rayan4444/assembly_line_wearable/REV1 - IMU BREAKOUT/TEST_DATA/TEST_SET_2_unscrewing/az.csv

Az
-0.19482421875
-0.19921875
-0.19140625
-0.20751953125
-0.189453125
-0.189453125
-0.19384765625
-0.2138671875
-0.17822265625
-0.15478515625
-0.16162109375
-0.17431640625
-0.142578125
-0.1796875
-0.0947265625
-0.03955078125
0.01171875
0.078125
0.08837890625
0.09521484375
0.14501953125
0.2041015625
0.31787109375
0.2509765625
0.2939453125
0.36474609375
0.365234375
0.4833984375
0.4892578125
0.50537109375
0.5537109375
0.57763671875
0.61279296875
0.58251953125
0.6171875
0.62744140625
0.64013671875
0.64208984375
0.673828125
0.75390625
0.78173828125
0.77734375
0.67138671875
0.6337890625
0.6083984375
0.64111328125
0.69384765625
0.7548828125
0.8095703125
0.8056640625
0.8212890625
0.81103515625
0.8037109375
0.66015625
0.775390625
0.7783203125
0.72802734375
0.73828125
0.76416015625
0.78076171875
0.78466796875
0.79296875
0.74072265625
0.74853515625
0.775390625
0.88330078125
0.59716796875
0.79541015625
0.72265625
0.80615234375
0.85791015625
0.8330078125
0.82177734375
0.81787109375
0.72509765625
1.24755859375
0.77880859375
0.83984375
0.71240234375
0.7275390625
0.7333984375
0.74365234375
0.62109375
0.69384765625
0.67333984375
0.74609375
0.7998046875
0.77734375
0.70751953125
0.75634765625
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
