rayan4444/assembly_line_wearable/REV1 - IMU BREAKOUT/TEST_DATA/TEST_SET_2_unscrewing/sensor_log.csv

Index | Timestamp | Ax | Ay | Az | Gx | Gy | Gz
1 | 2019-09-03 15:57:00 | 0.93798828125 | -0.08154296875 | -0.19482421875 | 0.7404580152671756 | 0.8091603053435115 | 0.8015267175572519
2 | 2019-09-03 15:57:00 | 0.9345703125 | -0.07958984375 | -0.19921875 | -0.061068702290076333 | 0.732824427480916 | 0.5877862595419847
3 | 2019-09-03 15:57:01 | 0.93359375 | -0.08447265625 | -0.19140625 | 0.9541984732824428 | 1.2213740458015268 | -0.08396946564885496
4 | 2019-09-03 15:57:01 | 0.92919921875 | -0.08203125 | -0.20751953125 | 0.0 | 1.786259541984733 | 0.6564885496183206
5 | 2019-09-03 15:57:01 | 0.93603515625 | -0.080078125 | -0.189453125 | 0.5648854961832062 | 0.9541984732824428 | 0.35877862595419846
6 | 2019-09-03 15:57:01 | 0.93505859375 | -0.08984375 | -0.189453125 | 0.32061068702290074 | 1.2900763358778626 | -1.1603053435114503
7 | 2019-09-03 15:57:01 | 0.9638671875 | -0.0830078125 | -0.19384765625 | 0.1984732824427481 | 2.1603053435114505 | -0.4961832061068702
8 | 2019-09-03 15:57:01 | 0.935546875 | -0.0947265625 | -0.2138671875 | -0.9541984732824428 | 4.358778625954199 | -1.2442748091603053
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
