rayan4444/assembly_line_wearable/REV1 - IMU BREAKOUT/TEST_DATA/TEST_SET_3_Unscrewing/ax.csv

Ax
0.91552734375
0.9072265625
0.94091796875
0.93701171875
0.92578125
0.958984375
0.96435546875
0.919921875
0.9599609375
0.9931640625
0.97705078125
0.95458984375
0.84375
0.88525390625
0.908203125
0.90625
0.8525390625
0.85205078125
0.880859375
0.83935546875
0.7431640625
0.82958984375
0.89892578125
0.8603515625
0.865234375
0.8828125
0.82421875
0.7490234375
0.68603515625
0.6083984375
0.5048828125
0.54833984375
0.36767578125
0.525390625
0.650390625
0.50048828125
0.4443359375
0.404296875
0.4384765625
0.4833984375
0.41796875
0.4013671875
0.4248046875
0.3984375
0.32080078125
0.3623046875
0.32080078125
0.30859375
0.37255859375
0.2919921875
0.3486328125
0.349609375
0.34765625
0.36767578125
0.349609375
0.34375
0.3251953125
0.3193359375
0.3076171875
0.28759765625
0.2763671875
0.265625
0.39697265625
0.40771484375
0.33349609375
0.30810546875
0.25732421875
0.29638671875
0.29150390625
0.29296875
0.11083984375
0.228515625
0.21044921875
0.21044921875
0.18603515625
0.21484375
0.15283203125
0.14111328125
0.33642578125
0.265625
0.18505859375
0.1474609375
0.3193359375
0.33935546875
0.1865234375
0.552734375
0.060546875
0.0107421875
0.5458984375
0.44384765625
0.14599609375
0.40673828125
0.1826171875
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
