rayan4444/assembly_line_wearable/REV1 - IMU BREAKOUT/TEST_DATA/TEST_SET_3_Unscrewing/ay.csv

Ay
0.169921875
0.1689453125
0.1591796875
0.17919921875
0.19140625
0.18896484375
0.1796875
0.220703125
0.1484375
0.14013671875
0.119140625
0.12158203125
0.15771484375
0.138671875
0.119140625
0.1181640625
0.09814453125
0.111328125
0.123046875
0.09765625
0.078125
0.0869140625
0.1025390625
0.0859375
0.052734375
0.07568359375
0.083984375
0.0654296875
-0.0146484375
-0.00341796875
0.00048828125
0.060546875
0.12841796875
0.07763671875
0.15185546875
0.1572265625
0.1591796875
0.1298828125
0.1220703125
0.08984375
0.0234375
0.08740234375
0.1083984375
0.162109375
-0.033203125
0.125
0.10009765625
0.12890625
0.09228515625
0.0986328125
0.12109375
0.09228515625
0.13232421875
0.14892578125
0.1787109375
0.15869140625
0.1240234375
0.09765625
0.1474609375
0.16650390625
0.21240234375
0.29296875
0.23974609375
0.22265625
0.169921875
0.14013671875
0.1689453125
0.1572265625
0.14453125
0.3427734375
0.2265625
0.21826171875
0.22265625
0.2080078125
0.185546875
0.21484375
0.314453125
0.23486328125
0.22021484375
0.23486328125
0.2099609375
0.19921875
0.25341796875
0.27587890625
0.30859375
0.408203125
0.30419921875
0.294921875
0.43994140625
0.38134765625
0.333984375
0.36962890625
0.10888671875
0.8203125
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
