rayan4444/assembly_line_wearable/REV3 - BT_IMU/Firmware/crimson_ble.c

#include "crimson_ble.h"

//includes based on uart example
#include <stdint.h>
#include <string.h>
#include "nrf.h"
#include "nrf_sdh.h"
#include "nrf_sdh_ble.h"
#include "nordic_common.h"
#include "app_error.h"
#include "app_timer.h"

#include "bsp_btn_ble.h"
#include "ble.h"
#include "ble_hci.h"
#include "ble_advdata.h"
#include "ble_advertising.h"
#include "ble_conn_params.h"
#include "ble_err.h"

#include "nrf_ble_gatt.h"
#include "nrf_ble_qwr.h"
#include "ble_nus.h"

#include "nrf_log.h"
#include "nrf_log_ctrl.h"
#include "nrf_log_default_backends.h"

//additional includes for cts_c service
#include "ble_db_discovery.h"
#include "ble_cts_c.h"
#include "peer_manager.h"
#include "peer_manager_handler.h"
#include "nrf_sdh_soc.h"

#define IS_SRVC_CHANGED_CHARACT_PRESENT 0 
#define NRF_BLE_MAX_MTU_SIZE            GATT_MTU_SIZE_DEFAULT 
#define APP_FEATURE_NOT_SUPPORTED       BLE_GATT_STATUS_ATTERR_APP_BEGIN + 2     

#define APP_BLE_CONN_CFG_TAG            1                                           /**< A tag identifying the SoftDevice BLE configuration. */

#define DEVICE_NAME                     "CRIMSON_TEST"                               /**< Name of device. Will be included in the advertising data. */
#define NUS_SERVICE_UUID_TYPE           BLE_UUID_TYPE_VENDOR_BEGIN                  /**< UUID type for the Nordic UART Service (vendor specific). */

#define APP_BLE_OBSERVER_PRIO           3                                           /**< Application's BLE observer priority. You shouldn't need to modify this value. */

#define APP_ADV_INTERVAL                64                                          /**< The advertising interval (in units of 0.625 ms. This value corresponds to 40 ms). */
#define APP_ADV_TIMEOUT_IN_SECONDS      180                                         /**< The advertising timeout (in units of seconds). */

#define APP_ADV_DURATION                18000                                       /**< The advertising duration (180 seconds) in units of 10 milliseconds. */

#define MIN_CONN_INTERVAL               MSEC_TO_UNITS(500, UNIT_1_25_MS)             /**< Minimum acceptable connection interval (20 ms), Connection interval uses 1.25 ms units. */
#define MAX_CONN_INTERVAL               MSEC_TO_UNITS(1000, UNIT_1_25_MS)             /**< Maximum acceptable connection interval (75 ms), Connection interval uses 1.25 ms units. */
#define SLAVE_LATENCY                   0                                           /**< Slave latency. */
#define CONN_SUP_TIMEOUT                MSEC_TO_UNITS(4000, UNIT_10_MS)             /**< Connection supervisory timeout (4 seconds), Supervision Timeout uses 10 ms units. */
#define FIRST_CONN_PARAMS_UPDATE_DELAY  APP_TIMER_TICKS(5000)                       /**< Time from initiating event (connect or start of notification) to first time sd_ble_gap_conn_param_update is called (5 seconds). */
#define NEXT_CONN_PARAMS_UPDATE_DELAY   APP_TIMER_TICKS(30000)                      /**< Time between each call to sd_ble_gap_conn_param_update after the first call (30 seconds). */
#define MAX_CONN_PARAMS_UPDATE_COUNT    3                                           /**< Number of attempts before giving up the connection parameter negotiation. */

// defines for secure connection things
#define SEC_PARAM_TIMEOUT               30                                          /**< Time-out for pairing request or security request (in seconds). */
#define SEC_PARAM_BOND                  1                                           /**< Perform bonding. */
#define SEC_PARAM_MITM                  0                                           /**< Man In The Middle protection requirement. */
#define SEC_PARAM_LESC                  0                                           /**< LE Secure Connections not enabled. */
#define SEC_PARAM_KEYPRESS              0                                           /**< Keypress notifications not enabled. */
#define SEC_PARAM_IO_CAPABILITIES       BLE_GAP_IO_CAPS_NONE                        /**< I/O capabilities. */
#define SEC_PARAM_OOB                   0                                           /**< Out Of Band data availability. */
#define SEC_PARAM_MIN_KEY_SIZE          7                                           /**< Minimum encryption key size. */
#define SEC_PARAM_MAX_KEY_SIZE          16 

#define DEAD_BEEF                       0xDEADBEEF    

BLE_NUS_DEF(m_nus, NRF_SDH_BLE_TOTAL_LINK_COUNT);  /**< BLE NUS service instance. */  
BLE_CTS_C_DEF(m_cts_c);                                                             /**< Current Time service instance. */                               
NRF_BLE_GATT_DEF(m_gatt);                                                           /**< GATT module instance. */
NRF_BLE_QWR_DEF(m_qwr);                                                             /**< Context for the Queued Write module.*/
BLE_ADVERTISING_DEF(m_advertising);
BLE_DB_DISCOVERY_DEF(m_ble_db_discovery);    
NRF_BLE_GQ_DEF(m_ble_gatt_queue,                                                    /**< BLE GATT Queue instance. */
               NRF_SDH_BLE_PERIPHERAL_LINK_COUNT,
               NRF_BLE_GQ_QUEUE_SIZE);                                       /**< DB discovery module instance. */

static ble_nus_t  m_nus;  
static uint16_t   m_conn_handle          = BLE_CONN_HANDLE_INVALID;                 /**< Handle of the current connection. */
static uint16_t   m_ble_nus_max_data_len = BLE_GATT_ATT_MTU_DEFAULT - 3;                        

static pm_peer_id_t m_peer_id;                                                      /**< Device reference handle to the current bonded central. */

static pm_peer_id_t m_whitelist_peers[BLE_GAP_WHITELIST_ADDR_MAX_COUNT];            /**< List of peers currently in the whitelist. */
static uint32_t     m_whitelist_peer_cnt;                                           /**< Number of peers currently in the whitelist. */


// YOUR_JOB: Use UUIDs for service(s) used in your application.
static ble_uuid_t m_adv_uuids[]          =                                          /**< Universally unique service identifier. */
{
    {BLE_UUID_NUS_SERVICE, NUS_SERVICE_UUID_TYPE},
    {BLE_UUID_CURRENT_TIME_SERVICE, BLE_UUID_TYPE_BLE}
};
// #define OUR_SENSOR_TIMER_INTERVAL     APP_TIMER_TICKS(1000, APP_TIMER_PRESCALER)     // 1000 ms intervals

// external functions to keep track of time (nrf_calendar)
void nrf_cal_set_time(uint32_t year, uint32_t month, uint32_t day, uint32_t hour, uint32_t minute, uint32_t second);

uint32_t year, month, day, hour, minute, second;
volatile bool time_synced= false; 
/**@brief Function for assert macro callback.
 *
 * @details This function will be called in case of an assert in the SoftDevice.
 *
 * @warning This handler is an example only and does not fit a final product. You need to analyse
 *          how your product is supposed to react in case of Assert.
 * @warning On assert from the SoftDevice, the system can only recover on reset.
 *
 * @param[in] line_num    Line number of the failing ASSERT call.
 * @param[in] p_file_name File name of the failing ASSERT call.
 */
void assert_nrf_callback(uint16_t line_num, const uint8_t * p_file_name)
{
    app_error_handler(DEAD_BEEF, line_num, p_file_name);
}

/**@brief Fetch the list of peer manager peer IDs.
 *
 * @param[inout] p_peers   The buffer where to store the list of peer IDs.
 * @param[inout] p_size    In: The size of the @p p_peers buffer.
 *                         Out: The number of peers copied in the buffer.
 */
static void peer_list_get(pm_peer_id_t * p_peers, uint32_t * p_size)
{
    pm_peer_id_t peer_id;
    uint32_t     peers_to_copy;

    peers_to_copy = (*p_size < BLE_GAP_WHITELIST_ADDR_MAX_COUNT) ?
                     *p_size : BLE_GAP_WHITELIST_ADDR_MAX_COUNT;

    peer_id = pm_next_peer_id_get(PM_PEER_ID_INVALID);
    *p_size = 0;

    while ((peer_id != PM_PEER_ID_INVALID) && (peers_to_copy--))
    {
        p_peers[(*p_size)++] = peer_id;
        peer_id = pm_next_peer_id_get(peer_id);
    }
}

/**@brief Clear bond information from persistent storage.
 */
static void delete_bonds(void)
{
    ret_code_t err_code;

    NRF_LOG_INFO("Erase bonds!");

    err_code = pm_peers_delete();
    APP_ERROR_CHECK(err_code);
}

/**@brief Function for handling Peer Manager events.
 *
 * @param[in] p_evt  Peer Manager event.
 */
static void pm_evt_handler(pm_evt_t const * p_evt)
{
    ret_code_t err_code;

    pm_handler_on_pm_evt(p_evt);
    pm_handler_flash_clean(p_evt);

    switch (p_evt->evt_id)
    {
        case PM_EVT_CONN_SEC_SUCCEEDED:
        {
            m_peer_id = p_evt->peer_id;

            // Discover peer's services.
            err_code  = ble_db_discovery_start(&m_ble_db_discovery, p_evt->conn_handle);
            APP_ERROR_CHECK(err_code);
        } break;

        case PM_EVT_PEERS_DELETE_SUCCEEDED:
        {
            advertising_start(false);
        } break;

        case PM_EVT_PEER_DATA_UPDATE_SUCCEEDED:
        {
            // Note: You should check on what kind of white list policy your application should use.
            if (     p_evt->params.peer_data_update_succeeded.flash_changed
                 && (p_evt->params.peer_data_update_succeeded.data_id == PM_PEER_DATA_ID_BONDING))
            {
                NRF_LOG_DEBUG("New Bond, add the peer to the whitelist if possible");
                NRF_LOG_DEBUG("\tm_whitelist_peer_cnt %d, MAX_PEERS_WLIST %d",
                               m_whitelist_peer_cnt + 1,
                               BLE_GAP_WHITELIST_ADDR_MAX_COUNT);

                if (m_whitelist_peer_cnt < BLE_GAP_WHITELIST_ADDR_MAX_COUNT)
                {
                    // Bonded to a new peer, add it to the whitelist.
                    m_whitelist_peers[m_whitelist_peer_cnt++] = m_peer_id;

                    // The whitelist has been modified, update it in the Peer Manager.
                    err_code = pm_device_identities_list_set(m_whitelist_peers, m_whitelist_peer_cnt);
                    if (err_code != NRF_ERROR_NOT_SUPPORTED)
                    {
                        APP_ERROR_CHECK(err_code);
                    }

                    err_code = pm_whitelist_set(m_whitelist_peers, m_whitelist_peer_cnt);
                    APP_ERROR_CHECK(err_code);
                }
            }
        } break;

        default:
            break;
    }
}

/**@brief Function for handling the Current Time Service errors.
 *
 * @param[in]  nrf_error  Error code containing information about what went wrong.
 */
static void current_time_error_handler(uint32_t nrf_error)
{
    APP_ERROR_HANDLER(nrf_error);
}

static void current_time_print(ble_cts_c_evt_t * p_evt)
{
    NRF_LOG_INFO("\r\nCurrent Time:");
   
    day  = (uint32_t)(p_evt->params.current_time.exact_time_256.day_date_time.date_time.day);
    printf("day: %ld\n", day);
    
    month = (uint32_t)(p_evt->params.current_time.exact_time_256.day_date_time.date_time.month);
    printf("month: %ld\n", month);

    year= (uint32_t) (p_evt->params.current_time.exact_time_256.day_date_time.date_time.year);
    printf("year: %ld\n", year);

    hour= (uint32_t)(p_evt->params.current_time.exact_time_256.day_date_time.date_time.hours);
    printf("hour: %ld\n",hour );

    minute=(uint32_t)(p_evt->params.current_time.exact_time_256.day_date_time.date_time.minutes);
    printf("minute: %ld\n", minute);

    second=(uint32_t)(p_evt->params.current_time.exact_time_256.day_date_time.date_time.seconds);
    printf("second: %ld\n", second);

    nrf_cal_set_time(year, month, day, hour, minute, second);
}

/**@brief Function for handling the Current Time Service client events.
 *
 * @details This function will be called for all events in the Current Time Service client that
 *          are passed to the application.
 *
 * @param[in] p_evt Event received from the Current Time Service client.
 */
static void on_cts_c_evt(ble_cts_c_t * p_cts, ble_cts_c_evt_t * p_evt)
{
    ret_code_t err_code;

    switch (p_evt->evt_type)
    {
        case BLE_CTS_C_EVT_DISCOVERY_COMPLETE:
            NRF_LOG_INFO("Current Time Service discovered on server.");
            err_code = ble_cts_c_handles_assign(&m_cts_c,
                                                p_evt->conn_handle,
                                                &p_evt->params.char_handles);
            APP_ERROR_CHECK(err_code);
            break;

        case BLE_CTS_C_EVT_DISCOVERY_FAILED:
            NRF_LOG_INFO("Current Time Service not found on server. ");
            // CTS not found in this case we just disconnect. There is no reason to stay
            // in the connection for this simple app since it all wants is to interact with CT
            if (p_evt->conn_handle != BLE_CONN_HANDLE_INVALID)
            {
                err_code = sd_ble_gap_disconnect(p_evt->conn_handle,
                                                 BLE_HCI_REMOTE_USER_TERMINATED_CONNECTION);
                APP_ERROR_CHECK(err_code);
            }
            break;

        case BLE_CTS_C_EVT_DISCONN_COMPLETE:
            NRF_LOG_INFO("Disconnect Complete.");
            break;

        case BLE_CTS_C_EVT_CURRENT_TIME:
            NRF_LOG_INFO("Current Time received.");
            current_time_print(p_evt);
            break;

        case BLE_CTS_C_EVT_INVALID_TIME:
            NRF_LOG_INFO("Invalid Time received.");
            break;

        default:
            break;
    }
}


/**@brief Function for the GAP initialization.
 *
 * @details This function will set up all the necessary GAP (Generic Access Profile) parameters of
 *          the device. It also sets the permissions and appearance.
 */
static void gap_params_init(void)
{
    uint32_t                err_code;
    ble_gap_conn_params_t   gap_conn_params;
    ble_gap_conn_sec_mode_t sec_mode;

    BLE_GAP_CONN_SEC_MODE_SET_OPEN(&sec_mode);

    err_code = sd_ble_gap_device_name_set(&sec_mode,
                                          (const uint8_t *) DEVICE_NAME,
                                          strlen(DEVICE_NAME));
    APP_ERROR_CHECK(err_code);

    memset(&gap_conn_params, 0, sizeof(gap_conn_params));

    gap_conn_params.min_conn_interval = MIN_CONN_INTERVAL;
    gap_conn_params.max_conn_interval = MAX_CONN_INTERVAL;
    gap_conn_params.slave_latency     = SLAVE_LATENCY;
    gap_conn_params.conn_sup_timeout  = CONN_SUP_TIMEOUT;

    err_code = sd_ble_gap_ppcp_set(&gap_conn_params);
    APP_ERROR_CHECK(err_code);
}

/**@brief Function for handling Queued Write Module errors.
 *
 * @details A pointer to this function will be passed to each service which may need to inform the
 *          application about an error.
 *
 * @param[in]   nrf_error   Error code containing information about what went wrong.
 */
static void nrf_qwr_error_handler(uint32_t nrf_error)
{
    APP_ERROR_HANDLER(nrf_error);
}

/**@brief Function for handling the data from the Nordic UART Service.
 *
 * @details This function will process the data received from the Nordic UART BLE Service and send
 *          it to the UART module.
 *
 * @param[in] p_evt       Nordic UART Service event.
 */
/**@snippet [Handling the data received over BLE] */
static void nus_data_handler(ble_nus_evt_t * p_evt)
{

    if (p_evt->type == BLE_NUS_EVT_RX_DATA)
    {
        uint32_t err_code;

        NRF_LOG_DEBUG("Received data from BLE NUS. Writing data on UART.");
        NRF_LOG_HEXDUMP_DEBUG(p_evt->params.rx_data.p_data, p_evt->params.rx_data.length);

        for (uint32_t i = 0; i < p_evt->params.rx_data.length; i++)
        {
            do
            {
                err_code = app_uart_put(p_evt->params.rx_data.p_data[i]);
                if ((err_code != NRF_SUCCESS) && (err_code != NRF_ERROR_BUSY))
                {
                    NRF_LOG_ERROR("Failed receiving NUS message. Error 0x%x. ", err_code);
                    APP_ERROR_CHECK(err_code);
                }
            } while (err_code == NRF_ERROR_BUSY);
        }
        if (p_evt->params.rx_data.p_data[p_evt->params.rx_data.length - 1] == '\r')
        {
            while (app_uart_put('\n') == NRF_ERROR_BUSY);
        }
    }

}
/**@snippet [Handling the data received over BLE] */


/**@brief   Function for handling app_uart events.
 *
 * @details This function will receive a single character from the app_uart module and append it to
 *          a string. The string will be be sent over BLE when the last character received was a
 *          'new line' '\n' (hex 0x0A) or if the string has reached the maximum data length.
 */
/**@snippet [Handling the data received over UART] */
void uart_event_handle(app_uart_evt_t * p_event)
{
    static uint8_t data_array[BLE_NUS_MAX_DATA_LEN];
    static uint8_t index = 0;
    uint32_t       err_code;

    switch (p_event->evt_type)
    {
        case APP_UART_DATA_READY:
            UNUSED_VARIABLE(app_uart_get(&data_array[index]));
            index++;

            if ((data_array[index - 1] == '\n') ||
                (data_array[index - 1] == '\r') ||
                (index >= m_ble_nus_max_data_len))
            {
                if (index > 1)
                {
                    NRF_LOG_DEBUG("Ready to send data over BLE NUS");
                    NRF_LOG_HEXDUMP_DEBUG(data_array, index);

                    do
                    {
                        uint16_t length = (uint16_t)index;
                        err_code = ble_nus_data_send(&m_nus, data_array, &length, m_conn_handle);
                        if ((err_code != NRF_ERROR_INVALID_STATE) &&
                            (err_code != NRF_ERROR_RESOURCES) &&
                            (err_code != NRF_ERROR_NOT_FOUND))
                        {
                            APP_ERROR_CHECK(err_code);
                        }
                    } while (err_code == NRF_ERROR_RESOURCES);
                }

                index = 0;
            }
            break;

        case APP_UART_COMMUNICATION_ERROR:
            APP_ERROR_HANDLER(p_event->data.error_communication);
            break;

        case APP_UART_FIFO_ERROR:
            APP_ERROR_HANDLER(p_event->data.error_code);
            break;

        default:
            break;
    }
}
/**@snippet [Handling the data received over UART] */

/**@brief Function for initializing services that will be used by the application.
 */
static void services_init(void)
{
    uint32_t           err_code;
    ble_nus_init_t     nus_init;
    ble_cts_c_init_t   cts_init = {0};
    nrf_ble_qwr_init_t qwr_init = {0};

    // Initialize Queued Write Module.
    qwr_init.error_handler = nrf_qwr_error_handler;

    err_code = nrf_ble_qwr_init(&m_qwr, &qwr_init);
    APP_ERROR_CHECK(err_code);

    // Initialize CTS.
    cts_init.evt_handler   = on_cts_c_evt;
    cts_init.error_handler = current_time_error_handler;
    cts_init.p_gatt_queue  = &m_ble_gatt_queue;
    err_code               = ble_cts_c_init(&m_cts_c, &cts_init);
    APP_ERROR_CHECK(err_code);

    // Initialize NUS.
    memset(&nus_init, 0, sizeof(nus_init));

    nus_init.data_handler = nus_data_handler;

    err_code = ble_nus_init(&m_nus, &nus_init);
    APP_ERROR_CHECK(err_code);

}

/**@brief Function for handling an event from the Connection Parameters Module.
 *
 * @details This function will be called for all events in the Connection Parameters Module
 *          which are passed to the application.
 *
 * @note All this function does is to disconnect. This could have been done by simply setting
 *       the disconnect_on_fail config parameter, but instead we use the event handler
 *       mechanism to demonstrate its use.
 *
 * @param[in] p_evt  Event received from the Connection Parameters Module.
 */
static void on_conn_params_evt(ble_conn_params_evt_t * p_evt)
{
    uint32_t err_code;

    if (p_evt->evt_type == BLE_CONN_PARAMS_EVT_FAILED)
    {
        err_code = sd_ble_gap_disconnect(m_conn_handle, BLE_HCI_CONN_INTERVAL_UNACCEPTABLE);
        APP_ERROR_CHECK(err_code);
    }
}

/**@brief Function for handling errors from the Connection Parameters module.
 *
 * @param[in] nrf_error  Error code containing information about what went wrong.
 */
static void conn_params_error_handler(uint32_t nrf_error)
{
    APP_ERROR_HANDLER(nrf_error);
}


/**@brief Function for initializing the Connection Parameters module.
 */
static void conn_params_init(void)
{
    uint32_t               err_code;
    ble_conn_params_init_t cp_init;

    memset(&cp_init, 0, sizeof(cp_init));

    cp_init.p_conn_params                  = NULL;
    cp_init.first_conn_params_update_delay = FIRST_CONN_PARAMS_UPDATE_DELAY;
    cp_init.next_conn_params_update_delay  = NEXT_CONN_PARAMS_UPDATE_DELAY;
    cp_init.max_conn_params_update_count   = MAX_CONN_PARAMS_UPDATE_COUNT;
    cp_init.start_on_notify_cccd_handle    = BLE_GATT_HANDLE_INVALID;
    cp_init.disconnect_on_fail             = false;
    cp_init.evt_handler                    = on_conn_params_evt;
    cp_init.error_handler                  = conn_params_error_handler;

    err_code = ble_conn_params_init(&cp_init);
    APP_ERROR_CHECK(err_code);
}

/**@brief Function for handling Database Discovery events.
 *
 * @details This function is a callback function to handle events from the database discovery module.
 *          Depending on the UUIDs that are discovered, this function should forward the events
 *          to their respective service instances.
 *
 * @param[in] p_event  Pointer to the database discovery event.
 */
static void db_disc_handler(ble_db_discovery_evt_t * p_evt)
{
    ble_cts_c_on_db_disc_evt(&m_cts_c, p_evt);
}

/**@brief Function for putting the chip into sleep mode.
 *
 * @note This function will not return.
 */
static void sleep_mode_enter(void)
{
    uint32_t err_code = bsp_indication_set(BSP_INDICATE_IDLE);
    APP_ERROR_CHECK(err_code);

    // Prepare wakeup buttons.
    err_code = bsp_btn_ble_sleep_mode_prepare();
    APP_ERROR_CHECK(err_code);

    // Go to system-off mode (this function will not return; wakeup will cause a reset).
    err_code = sd_power_system_off();
    APP_ERROR_CHECK(err_code);
}

/**@brief Function for handling advertising events.
 *
 * @details This function will be called for advertising events which are passed to the application.
 *
 * @param[in] ble_adv_evt  Advertising event.
 */
static void on_adv_evt(ble_adv_evt_t ble_adv_evt)
{
    uint32_t err_code;

    switch (ble_adv_evt)
    {
        case BLE_ADV_EVT_FAST:
            err_code = bsp_indication_set(BSP_INDICATE_ADVERTISING);
            APP_ERROR_CHECK(err_code);
            break;

        case BLE_ADV_EVT_SLOW:
            NRF_LOG_INFO("Slow advertising");
            err_code = bsp_indication_set(BSP_INDICATE_ADVERTISING_SLOW);
            APP_ERROR_CHECK(err_code);
            break;

        case BLE_ADV_EVT_FAST_WHITELIST:
            NRF_LOG_INFO("Fast advertising with WhiteList");
            err_code = bsp_indication_set(BSP_INDICATE_ADVERTISING_WHITELIST);
            APP_ERROR_CHECK(err_code);
            break;
        
        case BLE_ADV_EVT_SLOW_WHITELIST:
            NRF_LOG_INFO("Slow advertising with WhiteList");
            err_code = bsp_indication_set(BSP_INDICATE_ADVERTISING_WHITELIST);
            APP_ERROR_CHECK(err_code);
            err_code = ble_advertising_restart_without_whitelist(&m_advertising);
            APP_ERROR_CHECK(err_code);
            break;

        case BLE_ADV_EVT_IDLE:
            sleep_mode_enter();
            break;
        
        case BLE_ADV_EVT_WHITELIST_REQUEST:
        {
            ble_gap_addr_t whitelist_addrs[BLE_GAP_WHITELIST_ADDR_MAX_COUNT];
            ble_gap_irk_t  whitelist_irks[BLE_GAP_WHITELIST_ADDR_MAX_COUNT];
            uint32_t       addr_cnt = BLE_GAP_WHITELIST_ADDR_MAX_COUNT;
            uint32_t       irk_cnt  = BLE_GAP_WHITELIST_ADDR_MAX_COUNT;

            err_code = pm_whitelist_get(whitelist_addrs, &addr_cnt,
                                        whitelist_irks,  &irk_cnt);
            APP_ERROR_CHECK(err_code);
            NRF_LOG_DEBUG("pm_whitelist_get returns %d addr in whitelist and %d irk whitelist",
                           addr_cnt,
                           irk_cnt);

            // Apply the whitelist.
            err_code = ble_advertising_whitelist_reply(&m_advertising,
                                                       whitelist_addrs,
                                                       addr_cnt,
                                                       whitelist_irks,
                                                       irk_cnt);
            APP_ERROR_CHECK(err_code);
        }
        break;


        default:
            break;
    }
}

/**@brief Function for handling BLE events.
 *
 * @param[in]   p_ble_evt   Bluetooth stack event.
 * @param[in]   p_context   Unused.
 */
static void ble_evt_handler(ble_evt_t const * p_ble_evt, void * p_context)
{
    uint32_t err_code;
    pm_handler_secure_on_connection(p_ble_evt);

    switch (p_ble_evt->header.evt_id)
    {
        case BLE_GAP_EVT_CONNECTED:
            NRF_LOG_INFO("Connected");
            err_code = bsp_indication_set(BSP_INDICATE_CONNECTED);
            APP_ERROR_CHECK(err_code);
            m_conn_handle = p_ble_evt->evt.gap_evt.conn_handle;
            err_code = nrf_ble_qwr_conn_handle_assign(&m_qwr, m_conn_handle);
            APP_ERROR_CHECK(err_code);
            break;

        case BLE_GAP_EVT_DISCONNECTED:
            NRF_LOG_INFO("Disconnected");
            // LED indication will be changed when advertising starts.
            if (p_ble_evt->evt.gap_evt.conn_handle == m_cts_c.conn_handle)
            {

                m_cts_c.conn_handle = BLE_CONN_HANDLE_INVALID;
            } 
            m_conn_handle = BLE_CONN_HANDLE_INVALID;

            break;

        case BLE_GAP_EVT_PHY_UPDATE_REQUEST:
        {
            NRF_LOG_DEBUG("PHY update request.");
            ble_gap_phys_t const phys =
            {
                .rx_phys = BLE_GAP_PHY_AUTO,
                .tx_phys = BLE_GAP_PHY_AUTO,
            };
            err_code = sd_ble_gap_phy_update(p_ble_evt->evt.gap_evt.conn_handle, &phys);
            APP_ERROR_CHECK(err_code);
        } break;

        // case BLE_GAP_EVT_SEC_PARAMS_REQUEST:
        //     // Pairing not supported
        //     err_code = sd_ble_gap_sec_params_reply(m_conn_handle, BLE_GAP_SEC_STATUS_PAIRING_NOT_SUPP, NULL, NULL);
        //     APP_ERROR_CHECK(err_code);
        //     break;

        case BLE_GATTS_EVT_SYS_ATTR_MISSING:
            // No system attributes have been stored.
            err_code = sd_ble_gatts_sys_attr_set(m_conn_handle, NULL, 0, 0);
            APP_ERROR_CHECK(err_code);
            break;

        case BLE_GATTC_EVT_TIMEOUT:
            // Disconnect on GATT Client timeout event.
            err_code = sd_ble_gap_disconnect(p_ble_evt->evt.gattc_evt.conn_handle,
                                             BLE_HCI_REMOTE_USER_TERMINATED_CONNECTION);
            APP_ERROR_CHECK(err_code);
            break;

        case BLE_GATTS_EVT_TIMEOUT:
            // Disconnect on GATT Server timeout event.
            err_code = sd_ble_gap_disconnect(p_ble_evt->evt.gatts_evt.conn_handle,
                                             BLE_HCI_REMOTE_USER_TERMINATED_CONNECTION);
            APP_ERROR_CHECK(err_code);
            break;

        case BLE_EVT_USER_MEM_REQUEST:
            err_code = sd_ble_user_mem_reply(p_ble_evt->evt.gattc_evt.conn_handle, NULL);
            APP_ERROR_CHECK(err_code);
            break; // BLE_EVT_USER_MEM_REQUEST
        
        case BLE_GATTS_EVT_RW_AUTHORIZE_REQUEST:
        {
            ble_gatts_evt_rw_authorize_request_t  req;
            ble_gatts_rw_authorize_reply_params_t auth_reply;

            req = p_ble_evt->evt.gatts_evt.params.authorize_request;

            if (req.type != BLE_GATTS_AUTHORIZE_TYPE_INVALID)
            {
                if ((req.request.write.op == BLE_GATTS_OP_PREP_WRITE_REQ)     ||
                    (req.request.write.op == BLE_GATTS_OP_EXEC_WRITE_REQ_NOW) ||
                    (req.request.write.op == BLE_GATTS_OP_EXEC_WRITE_REQ_CANCEL))
                {
                    if (req.type == BLE_GATTS_AUTHORIZE_TYPE_WRITE)
                    {
                        auth_reply.type = BLE_GATTS_AUTHORIZE_TYPE_WRITE;
                    }
                    else
                    {
                        auth_reply.type = BLE_GATTS_AUTHORIZE_TYPE_READ;
                    }
                    auth_reply.params.write.gatt_status = APP_FEATURE_NOT_SUPPORTED;
                    err_code = sd_ble_gatts_rw_authorize_reply(p_ble_evt->evt.gatts_evt.conn_handle,
                                                               &auth_reply);
                    APP_ERROR_CHECK(err_code);
                }
            }
        } break; // BLE_GATTS_EVT_RW_AUTHORIZE_REQUEST


        default:
            // No implementation needed.
            break;
    }
}


/**@brief Function for the SoftDevice initialization.
 *
 * @details This function initializes the SoftDevice and the BLE event interrupt.
 */
static void ble_stack_init(void)
{
    ret_code_t err_code;

    err_code = nrf_sdh_enable_request();
    APP_ERROR_CHECK(err_code);

    // Configure the BLE stack using the default settings.
    // Fetch the start address of the application RAM.
    uint32_t ram_start = 0;
    err_code = nrf_sdh_ble_default_cfg_set(APP_BLE_CONN_CFG_TAG, &ram_start);
    APP_ERROR_CHECK(err_code);

    // Enable BLE stack.
    err_code = nrf_sdh_ble_enable(&ram_start);
    APP_ERROR_CHECK(err_code);

    // Register a handler for BLE events.
    NRF_SDH_BLE_OBSERVER(m_ble_observer, APP_BLE_OBSERVER_PRIO, ble_evt_handler, NULL);
}


/**@brief Function for handling events from the GATT library. */
void gatt_evt_handler(nrf_ble_gatt_t * p_gatt, nrf_ble_gatt_evt_t const * p_evt)
{
    if ((m_conn_handle == p_evt->conn_handle) && (p_evt->evt_id == NRF_BLE_GATT_EVT_ATT_MTU_UPDATED))
    {
        m_ble_nus_max_data_len = p_evt->params.att_mtu_effective - OPCODE_LENGTH - HANDLE_LENGTH;
        NRF_LOG_INFO("Data len is set to 0x%X(%d)", m_ble_nus_max_data_len, m_ble_nus_max_data_len);
    }
    NRF_LOG_DEBUG("ATT MTU exchange completed. central 0x%x peripheral 0x%x",
                  p_gatt->att_mtu_desired_central,
                  p_gatt->att_mtu_desired_periph);
}


/**@brief Function for initializing the GATT library. */
void gatt_init(void)
{
    ret_code_t err_code;

    err_code = nrf_ble_gatt_init(&m_gatt, gatt_evt_handler);
    APP_ERROR_CHECK(err_code);

    err_code = nrf_ble_gatt_att_mtu_periph_set(&m_gatt, NRF_SDH_BLE_GATT_MAX_MTU_SIZE);
    APP_ERROR_CHECK(err_code);
}


/**@brief Function for handling events from the BSP module.
 *
 * @param[in]   event   Event generated by button press.
 */
void bsp_event_handler(bsp_event_t event)
{
    uint32_t err_code;
    switch (event)
    {
        case BSP_EVENT_SLEEP:
            sleep_mode_enter();
            break;

        case BSP_EVENT_DISCONNECT:
            err_code = sd_ble_gap_disconnect(m_conn_handle, BLE_HCI_REMOTE_USER_TERMINATED_CONNECTION);
            if (err_code != NRF_ERROR_INVALID_STATE)
            {
                APP_ERROR_CHECK(err_code);
            }
            break;

        case BSP_EVENT_WHITELIST_OFF:
            if (m_cts_c.conn_handle == BLE_CONN_HANDLE_INVALID)
            {
                err_code = ble_advertising_restart_without_whitelist(&m_advertising);
                if (err_code != NRF_ERROR_INVALID_STATE)
                {
                    APP_ERROR_CHECK(err_code);
                }
            }
            break;

        case BSP_EVENT_KEY_0:
            if (m_cts_c.conn_handle != BLE_CONN_HANDLE_INVALID)
            {
                err_code = ble_cts_c_current_time_read(&m_cts_c);
                time_synced= true; 

                if (err_code == NRF_ERROR_NOT_FOUND)
                {
                    NRF_LOG_INFO("Current Time Service is not discovered.");
                }
            }
            break;

        default:
            break;
    }
}



/**@brief Function for initializing the Advertising functionality.
 */
static void advertising_init(void)
{
    uint32_t               err_code;
    ble_advertising_init_t init;

    memset(&init, 0, sizeof(init));

    init.advdata.name_type          = BLE_ADVDATA_FULL_NAME;
    init.advdata.include_appearance = false;
    init.advdata.flags              = BLE_GAP_ADV_FLAGS_LE_ONLY_LIMITED_DISC_MODE;

    init.srdata.uuids_complete.uuid_cnt = sizeof(m_adv_uuids) / sizeof(m_adv_uuids[0]);
    init.srdata.uuids_complete.p_uuids  = m_adv_uuids;

    init.config.ble_adv_fast_enabled  = true;
    init.config.ble_adv_fast_interval = APP_ADV_INTERVAL;
    init.config.ble_adv_fast_timeout  = APP_ADV_DURATION;
    init.evt_handler = on_adv_evt;

    err_code = ble_advertising_init(&m_advertising, &init);
    APP_ERROR_CHECK(err_code);

    ble_advertising_conn_cfg_tag_set(&m_advertising, APP_BLE_CONN_CFG_TAG);
}

/**@brief Function for initializing buttons and leds.
 *
 * @param[out] p_erase_bonds  Will be true if the clear bonding button was pressed to wake the application up.
 */
static void buttons_leds_init(bool * p_erase_bonds)
{
    bsp_event_t startup_event;

    uint32_t err_code = bsp_init(BSP_INIT_LEDS | BSP_INIT_BUTTONS, bsp_event_handler);
    APP_ERROR_CHECK(err_code);

    err_code = bsp_btn_ble_init(NULL, &startup_event);
    APP_ERROR_CHECK(err_code);

    *p_erase_bonds = (startup_event == BSP_EVENT_CLEAR_BONDING_DATA);
}

/**@brief Function for the Peer Manager initialization.
 */
static void peer_manager_init(void)
{
    ble_gap_sec_params_t sec_param;
    ret_code_t           err_code;

    err_code = pm_init();
    APP_ERROR_CHECK(err_code);

    memset(&sec_param, 0, sizeof(ble_gap_sec_params_t));

    // Security parameters to be used for all security procedures.
    sec_param.bond           = SEC_PARAM_BOND;
    sec_param.mitm           = SEC_PARAM_MITM;
    sec_param.lesc           = SEC_PARAM_LESC;
    sec_param.keypress       = SEC_PARAM_KEYPRESS;
    sec_param.io_caps        = SEC_PARAM_IO_CAPABILITIES;
    sec_param.oob            = SEC_PARAM_OOB;
    sec_param.min_key_size   = SEC_PARAM_MIN_KEY_SIZE;
    sec_param.max_key_size   = SEC_PARAM_MAX_KEY_SIZE;
    sec_param.kdist_own.enc  = 1;
    sec_param.kdist_own.id   = 1;
    sec_param.kdist_peer.enc = 1;
    sec_param.kdist_peer.id  = 1;

    err_code = pm_sec_params_set(&sec_param);
    APP_ERROR_CHECK(err_code);

    err_code = pm_register(pm_evt_handler);
    APP_ERROR_CHECK(err_code);
}

/**
 * @brief Database discovery collector initialization.
 */
static void db_discovery_init(void)
{
    ble_db_discovery_init_t db_init;

    memset(&db_init, 0, sizeof(ble_db_discovery_init_t));

    db_init.evt_handler  = db_disc_handler;
    db_init.p_gatt_queue = &m_ble_gatt_queue;

    ret_code_t err_code = ble_db_discovery_init(&db_init);
    APP_ERROR_CHECK(err_code);
}

/**@brief Function for starting advertising.
 */
void advertising_start(bool erase_bonds)
{
    if (erase_bonds == true)
    {
        delete_bonds();
        // Advertising is started by PM_EVT_PEERS_DELETE_SUCCEEDED event.
    }
    else
    {
    ret_code_t ret;

    memset(m_whitelist_peers, PM_PEER_ID_INVALID, sizeof(m_whitelist_peers));
    m_whitelist_peer_cnt = (sizeof(m_whitelist_peers) / sizeof(pm_peer_id_t));

    peer_list_get(m_whitelist_peers, &m_whitelist_peer_cnt);

    ret = pm_whitelist_set(m_whitelist_peers, m_whitelist_peer_cnt);
    APP_ERROR_CHECK(ret);

    // Setup the device identies list.
    // Some SoftDevices do not support this feature.
    ret = pm_device_identities_list_set(m_whitelist_peers, m_whitelist_peer_cnt);
    if (ret != NRF_ERROR_NOT_SUPPORTED)
    {
        APP_ERROR_CHECK(ret);
    }

    ret = ble_advertising_start(&m_advertising, BLE_ADV_MODE_FAST);
    APP_ERROR_CHECK(ret);
}
}

void crimson_ble_init(void) {
    bool erase_bonds;
    
    buttons_leds_init(&erase_bonds);
    ble_stack_init();
    gap_params_init();
    gatt_init();
    db_discovery_init();
    services_init();
    advertising_init();
    peer_manager_init();
    conn_params_init();
    advertising_start(erase_bonds);

}
