rayan4444/assembly_line_wearable/REV3 - BT_IMU/Firmware/crimson_sdcard.h

#ifndef SD_CARD_
#define SD_CARD_
/**
 *
 * nRF52 SD card interface to log data.
 *
 * Electronut Labs
 * electronut.in
 */
#include "nrf.h"
#include "bsp.h"
#include "ff.h"
#include "diskio_blkdev.h"
#include "nrf_block_dev_sdc.h"
#include "app_sdcard.h"

#include "nrf_log.h"
#include "nrf_log_ctrl.h"
#include "nrf_log_default_backends.h"

#define FILE_NAME   "CRIMSON.TXT"
#define TEST_STRING "Crimson event data\r\n\n"

/**
 * @brief function to log data in SD card.
 */
void sdcard_init();
void sdcard_sensor_update_data(char * event_time, uint8_t event_type);

#endif //SD_CARD_
